peterokwara/BuildingManagement/esp/current-sensor/config.py

MQTT_CONFIG = {
    'SENSOR_ID': 'CURRENT_SENSOR',
    'MQTT_HOST': '192.168.0.179',
    'PORT': '1883',
    'PUB_TOPIC': 'building/room/power'
}

WIFI_CONFIG = {
    'WIFI_ESSID': 'skypee.exe',
    'WIFI_PASSWORD': 'R2HoPWodVvbJ'
}
