peterokwara/BuildingManagement/esp/relay-fan/config.py

MQTT_CONFIG = {
    'SENSOR_ID': 'FAN',
    'MQTT_HOST': '192.168.0.179',
    'PORT': '1883',
    'PUB_TOPIC': 'building/room/relay/fan',
}

WIFI_CONFIG = {
    'WIFI_ESSID': 'skypee.exe',
    'WIFI_PASSWORD': 'R2HoPWodVvbJ'
}
